3ecologias/iotrees/printed-circuit-0.6/iotress6_etch_silk_bottom.pdf

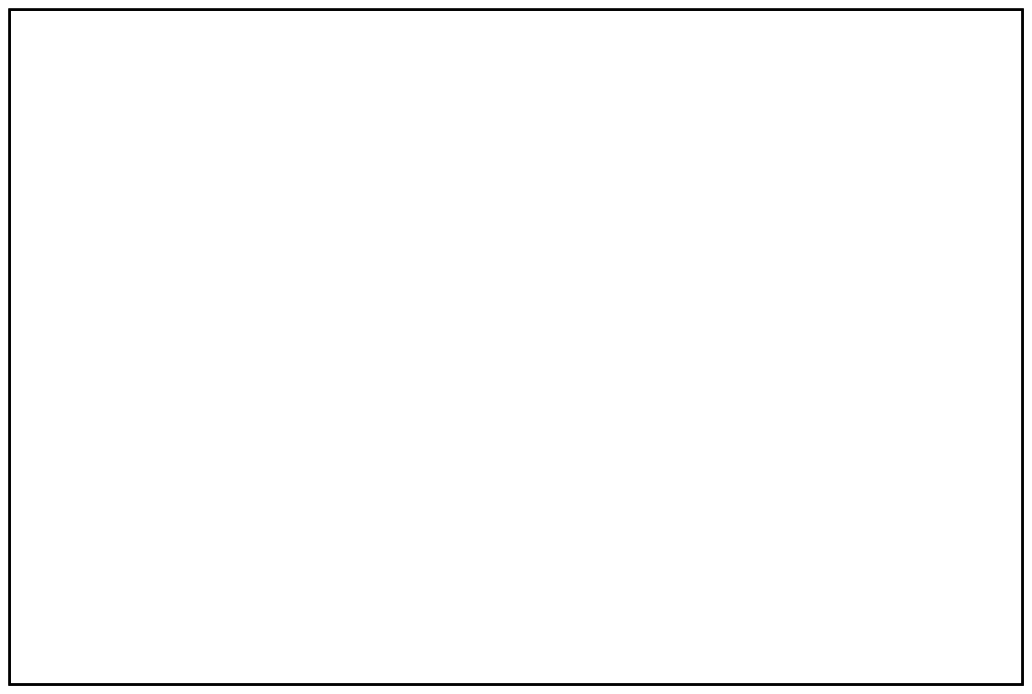
[picture p13: page 1]
