3ecologias/iotrees/printed-circuit-0.6/iotress6_etch_silk_top.pdf

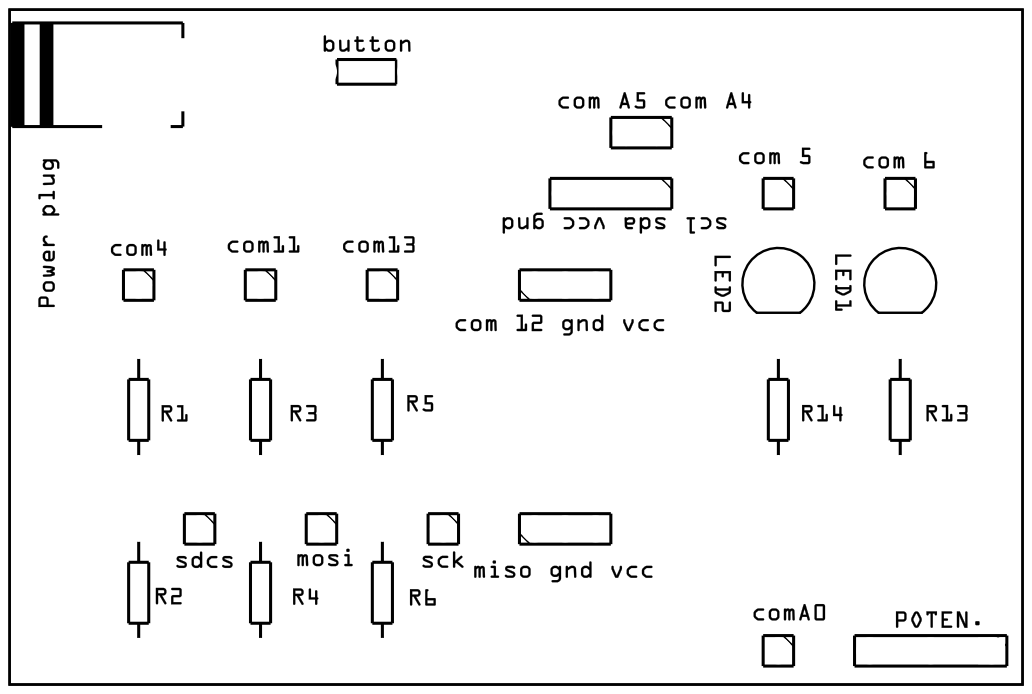
[picture p14: page 1]
