3ecologias/iotrees/printed-circuit-0.6/iotress6_etch_silk_top_mirror.pdf

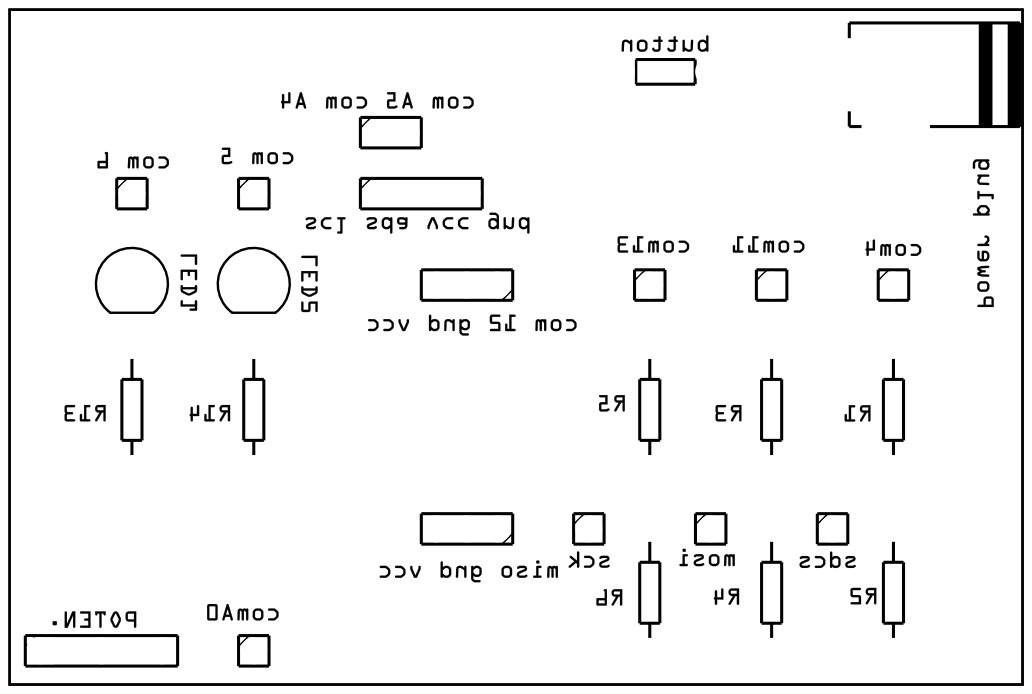
[picture p15: page 1]
